zdeager/powermod/hardware/tools/mount_best.py

UNROUTED=0
FLOORPLAN={'R19': (55.68, 15.0, 90), 'U2': (46.87, 12.0, 0), 'JP1': (60.0, 32.5, 0), 'R12': (13.24, 7.56, 0), 'R4': (48.97, 28.5, 0), 'Y1': (62.6, 11.01, 0), 'R3': (6.5, 22.13, 0), 'C16': (36.24, 11.0, 90), 'R16': (54.03, 20.01, 0), 'SW1': (32.0, 35.5, -90), 'R21': (27.53, 28.5, 0), 'R1': (10.74, 11.24, 0), 'J1': (4.9, 15.0, -90), 'D1': (25.5, 36.0, -90), 'C11': (45.01, 21.99, 0), 'R8': (19.75, 7.95, 0), 'R24': (25.6, 16.95, 0), 'R5': (51.03, 28.5, 0), 'R7': (7.26, 28.11, 0), 'JP2': (39.85, 32.5, 0), 'J3': (2.55, 35.5, 90), 'D3': (59.3, 15.0, 0), 'R27': (59.5, 18.0, 0), 'R28': (18.32, 15.5, 0), 'R26': (25.62, 19.4, 0), 'D2': (20.5, 36.0, -90), 'TP2': (12.5, 37.0, 0), 'TP3': (38.5, 37.0, 0), 'C14': (42.0, 21.56, 0), 'C1': (30.45, 7.68, 0), 'R20': (25.47, 25.0, 0), 'TP4': (15.5, 37.0, 0), 'Q3': (25.43, 14.08, 0), 'R11': (25.61, 10.84, 90), 'TP6': (41.5, 37.0, 0), 'U3': (33.45, 12.33, 0), 'R13': (27.26, 16.98, 90), 'C8': (20.6, 22.88, 0), 'R18': (56.82, 15.0, 90), 'L1': (33.28, 19.55, 180), 'R2': (6.5, 20.99, 0), 'R10': (23.47, 8.56, 0), 'C4': (30.14, 10.56, 90), 'C6': (11.29, 18.22, 0), 'C2': (34.05, 8.2, 0), 'Q1': (16.5, 9.95, 0), 'C5': (28.62, 14.16, 90), 'R25': (25.62, 18.1, 0), 'TP5': (61.5, 37.0, 0), 'R14': (36.71, 13.4, 0), 'R22': (12.39, 28.5, 0), 'C9': (24.4, 26.38, 0), 'C15': (11.43, 6.44, 0), 'C12': (23.51, 7.44, 0), 'R23': (22.53, 28.5, 0), 'R9': (25.52, 7.95, 0), 'J5': (14.0, 31.0, 90), 'C13': (55.0, 6.82, 0), 'J2': (50.0, 35.05, 0), 'C7': (8.62, 7.0, 0), 'R17': (54.0, 15.0, 90), 'D4': (62.7, 15.0, 0), 'C10': (42.99, 20.45, 0), 'C3': (27.26, 10.48, 90), 'R15': (51.97, 19.99, 0), 'TP1': (58.5, 37.0, 0), 'U5': (21.38, 16.31, 0), 'Q2': (19.52, 19.94, 0), 'U1': (56.7, 10.18, 0), 'J4': (18.5, 4.0, 180), 'U4': (13.5, 14.59, 0), 'R6': (14.42, 28.56, 0)}
